Circuit-killer/psmux/spice/main.asc

C1: polcap; 10µ; V=25 Irms=39m Rser=2.8 Lser=0 mfg="Nichicon" pn="UPR1E100MAH" type="Al electrolytic"
C2: polcap; 10µ; V=25 Irms=145m Rser=0.62 Lser=0
C3: polcap; 100µ; V=25 Irms=145m Rser=0.62 Lser=0 mfg="Nichicon" pn="UPR1E101MPH" type="Al electrolytic"
C4: polcap; 100µ; V=25 Irms=145m Rser=0.62 Lser=0 mfg="Nichicon" pn="UPR1E101MPH" type="Al electrolytic"
D1: schottky; 1N5817
D2: schottky; 1N5817
D3: schottky; BAT54
D4: schottky; BAT54
D5: schottky; BAT54
Q1: npn; 2N2222
Q2: npn; 2N2222
R1: res; 100K
R2: res; 100K
R3: res; 10K
R4: res; 10K
R6: res; 10
U1: irf540n
U2: irf540n
U3: SN74AHC1G00
U4: SN74AHC1G00
U7: SN74AHC1G00
V2: voltage; 11
V3: voltage; PULSE(0 3 0 0.000001 0.000001 0.00005 0.0001)
V4: voltage; PULSE(0 3 0.02 0.000001 0.000001 0.002 0.002 1)
V5: voltage; PULSE(0 3 0.00005 0.000001 0.000001 0.00005 0.0001)
V6: voltage; 14
V7: voltage; PULSE(0 3 0.021 0.000001 0.000001 0.002 0.002 1)
V8: voltage; 3
Named nets: POW1_V+, POW0_V+, 0, POW01_V+, BOOST_V+, DIS0, MCU_EN0, LOAD_V+, MCU_EN1, DIS1, LOGIC_V+, XCOND_EN
.tran 0 0.1 0
Dickson charge pump
OR redundancy
load
input: 0 - 5V
output: 0 - 5V, 20mA
no need for amplifier
